pfiliberti/pico_tnc/pico-pcb/pcb.kicad_sch

## KiCad design pico-pcb/pcb.kicad_sch (2026-09-22)

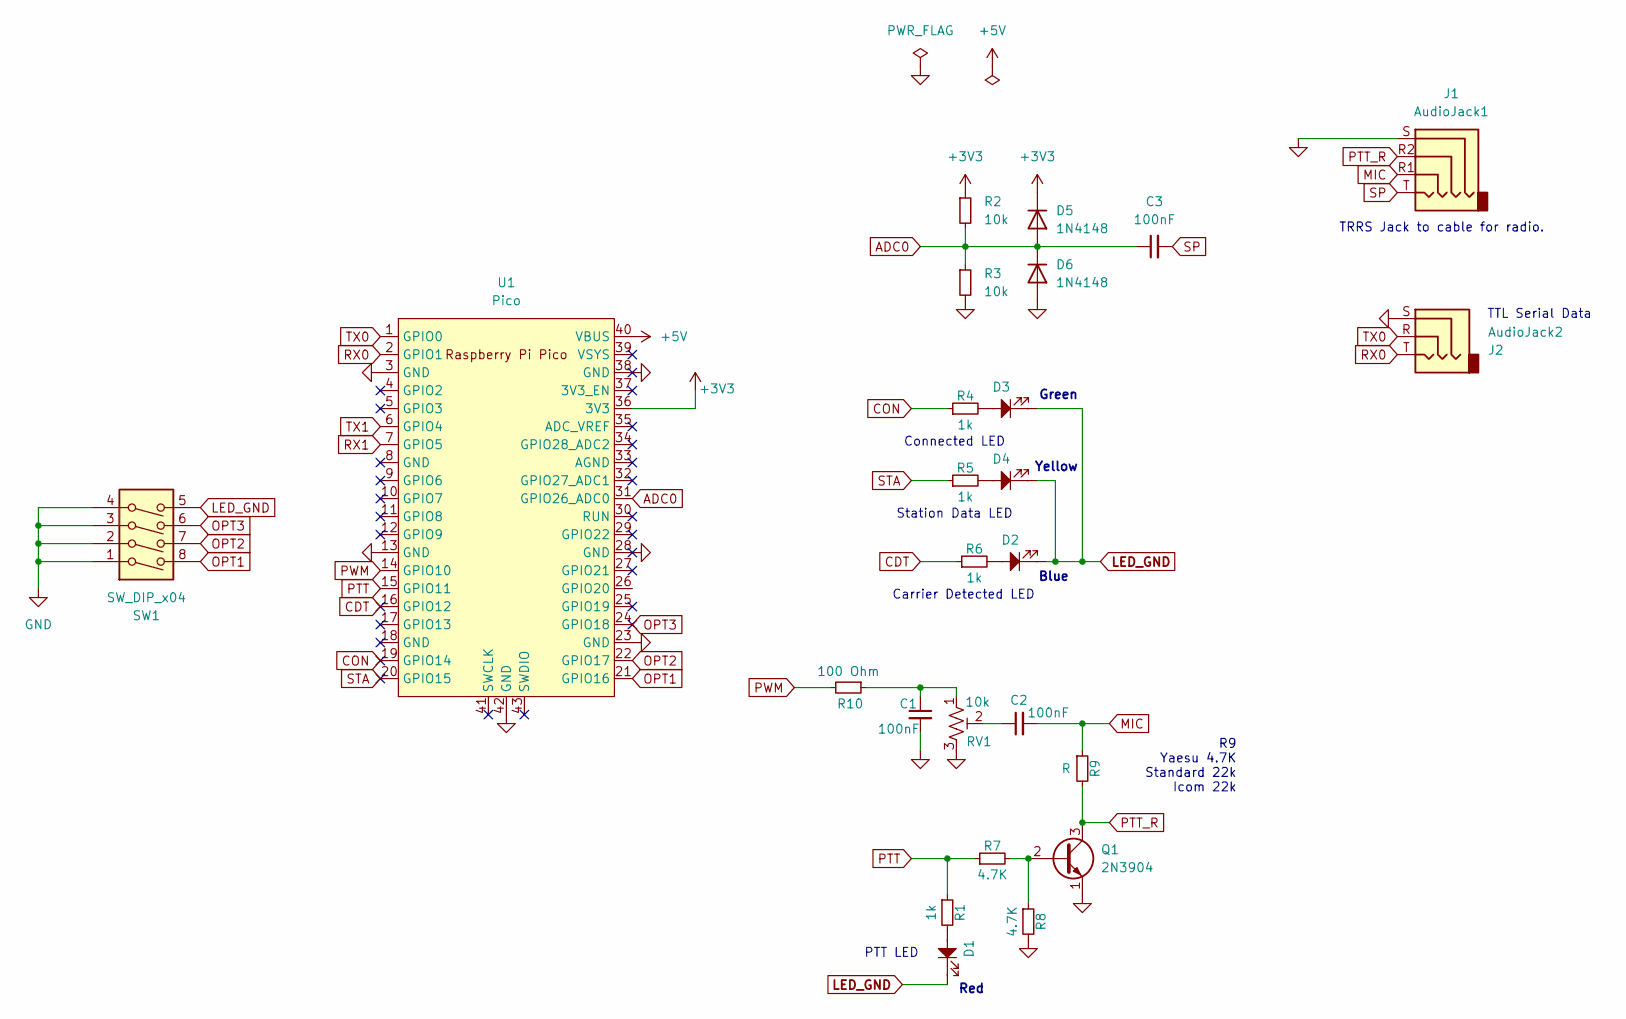
[picture p3: schematic pcb.kicad_sch]

Parts:
C1, C2, C3: 100nF; C_Disc_D3.0mm_W2.0mm_P2.50mm
D1, D2, D3, D4: LED_3mm; LED_D3.0mm_Horizontal_O1.27mm_Z2.0mm
D5, D6: 1N4148; D_DO-35_SOD27_P7.62mm_Horizontal
J1: AudioJack1; Jack_3.5mm_PJ320D_Horizontal
J2: AudioJack2; PJ-307
Q1: 2N3904; TO-92_Inline
R1, R4, R5, R6: 1k; R_Axial_DIN0204_L3.6mm_D1.6mm_P5.08mm_Horizontal
R2, R3: 10k; R_Axial_DIN0204_L3.6mm_D1.6mm_P5.08mm_Horizontal
R7, R8: 4.7K; R_Axial_DIN0204_L3.6mm_D1.6mm_P5.08mm_Horizontal
R9: R; R_Axial_DIN0204_L3.6mm_D1.6mm_P5.08mm_Horizontal
R10: 100 Ohm; R_Axial_DIN0204_L3.6mm_D1.6mm_P5.08mm_Horizontal
RV1: 10k; Potentiometer_Runtron_RM-063_Horizontal
SW1: SW_DIP_x04; SW_DIP_SPSTx04_Piano_CTS_Series194-4MSTN_W7.62mm_P2.54mm
U1: Pico; RPi_Pico_SMD_TH

Connections:
+3V3: D5.1 (K), R2.1, U1.36 (3V3)
+5V: U1.40 (VBUS)
ADC0: C3.1, D5.2 (A), D6.1 (K), R2.2, R3.1, U1.31 (GPIO26_ADC0)
CDT: R6.1, U1.16 (GPIO12)
CON: R4.1, U1.19 (GPIO14)
GND: C1.2, D6.2 (A), J1.S, J2.S, Q1.1 (E), R3.2, R8.2, RV1.3, SW1.1, SW1.2, SW1.3, SW1.4, U1.3 (GND), U1.13 (GND), U1.23 (GND), U1.28 (GND), U1.38 (GND), U1.42 (GND)
LED_GND: D1.1, D2.1, D3.1, D4.1, SW1.5
MIC: C2.2, J1.R1, R9.1
unnamed: C1.1, R10.1, RV1.1
unnamed: C2.1, RV1.2
unnamed: D1.2, R1.2
unnamed: D2.2, R6.2
unnamed: D3.2, R4.2
unnamed: D4.2, R5.2
unnamed: Q1.2 (B), R7.2, R8.1
OPT1: SW1.8, U1.21 (GPIO16)
OPT2: SW1.7, U1.22 (GPIO17)
OPT3: SW1.6, U1.24 (GPIO18)
PTT: R1.1, R7.1, U1.15 (GPIO11)
PTT_R: J1.R2, Q1.3 (C), R9.2
PWM: R10.2, U1.14 (GPIO10)
RX0: J2.T, U1.2 (GPIO1)
RX1: U1.7 (GPIO5)
SP: C3.2, J1.T
STA: R5.1, U1.20 (GPIO15)
TX0: J2.R, U1.1 (GPIO0)
TX1: U1.6 (GPIO4)

Notes on the sheet:
PTT LED
Carrier Detected LED
Yellow
Green
TRRS Jack to cable for radio.
Station Data LED
TTL Serial Data
Blue
Connected LED
R9 Yaesu 4.7K Standard 22k Icom 22k
Red
