pfiliberti/pico_tnc/pico_tnc/ax25.c

/*
Copyright (c) 2021, Kazuhisa Yokota, JN1DFF
All rights reserved.

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
THIS SOFTWARE IS PROVIDED BY THE COPYRIGHT HOLDERS AND CONTRIBUTORS "AS IS" AND
ANY EXPRESS OR IMPLIED WARRANTIES, INCLUDING, BUT NOT LIMITED TO, THE IMPLIED
WARRANTIES OF MERCHANTABILITY AND FITNESS FOR A PARTICULAR PURPOSE ARE
DISCLAIMED. IN NO EVENT SHALL <COPYRIGHT HOLDER> BE LIABLE FOR ANY
DIRECT, INDIRECT, INCIDENTAL, SPECIAL, EXEMPLARY, OR CONSEQUENTIAL DAMAGES
(INCLUDING, BUT NOT LIMITED TO, PROCUREMENT OF SUBSTITUTE GOODS OR SERVICES;
LOSS OF USE, DATA, OR PROFITS; OR BUSINESS INTERRUPTION) HOWEVER CAUSED AND
ON ANY THEORY OF LIABILITY, WHETHER IN CONTRACT, STRICT LIABILITY, OR TORT
(INCLUDING NEGLIGENCE OR OTHERWISE) ARISING IN ANY WAY OUT OF THE USE OF THIS
SOFTWARE, EVEN IF ADVISED OF THE POSSIBILITY OF SUCH DAMAGE.
*/

/*
    calculate CCITT-16 CRC using DMA CRC hardware
*/
#include <stdio.h>
#include "pico/stdlib.h"

#include "ax25.h"
#include "tnc.h" // Added by Codex


/* Input Queue to stack multiple incoming packets */
struct inQueue Ax25_In_Q[AX25_IN_MAXSIZE];
unsigned int Ax25_In_Head;
unsigned int Ax25_In_Tail;

//#ifdef RASPBERRYPI_PICO
#ifdef PICO_DEFAULT_UART

#include "hardware/dma.h"

#define OUT_INV (1 << 11)
#define OUT_REV (1 << 10)

int ax25_fcs(uint32_t crc, const uint8_t *data, int size)
{
    uint8_t dummy;
    int dma_chan = dma_claim_unused_channel(true);
    dma_channel_config c = dma_channel_get_default_config(dma_chan);

    channel_config_set_transfer_data_size(&c, DMA_SIZE_8);
    channel_config_set_write_increment(&c, false);
    channel_config_set_read_increment(&c, true);
    channel_config_set_dreq(&c, DREQ_FORCE);

    dma_channel_configure(
        dma_chan,
        &c,
        &dummy,
        data,
        size,
        false
    );

    // enable sniffer
    dma_sniffer_enable(dma_chan, 0x3, true);
    dma_hw->sniff_ctrl |= OUT_INV | OUT_REV;
    dma_hw->sniff_data = crc;
    dma_hw->sniff_data >>= 16;

    // start DMA
    dma_channel_start(dma_chan);

    // wait for finish
    dma_channel_wait_for_finish_blocking(dma_chan);
    dma_channel_unclaim(dma_chan);

    return dma_hw->sniff_data >> 16;
}

#else

#warning using C standard routine

#define CRC16_POLY 0x10811 /* G(x) = 1 + x^5 + x^12 + x^16 */

int ax25_fcs(uint32_t crc, const uint8_t packet[], int length)
{
    int i, j;

    if (length <= 0) return -1; // packet too short

    // calculate CRC x^16 + x^12 + x^5 + 1
    crc = 0xffff; /* initial value */
    for (i = 0; i < length; i++) {
	crc ^= packet[i];
	for (j = 0; j < 8; j++) {
	    if (crc & 1) crc ^= CRC16_POLY;
	    crc >>= 1;
	}
    }
    crc ^= 0xffff; // invert

    return crc;
}

#endif

bool ax25_callcmp(callsign_t *c, uint8_t *addr)
{
    for (int i = 0; i < 6; i++) {
        if (c->call[i] != (addr[i] >> 1)) return false;
    }

    if (c->ssid == ((addr[6] >> 1) & 0x0f)) return true;

    return false;
}

void ax25_mkax25addr(uint8_t *addr, callsign_t *c)
{
    uint8_t *s = addr;

    for (int i = 0; i < 6; i++) {
        *s++ = c->call[i] << 1;
    }

    // SSID
    *s = (c->ssid << 1) | 0x60;
}

bool ax25_ui(uint8_t *packet, int len)
{
    int i;

    i = AX25_ADDR_LEN - 1; // SSID
    while (i < len) {
        if (packet[i] & 1) break; // address extension bit
        i += AX25_ADDR_LEN;
    }
    i++;

    if (i + 2 > len) return false; // no control and  PID field

    return packet[i] == 0x03 && packet[i+1] == 0xf0; // true if UI packet
}

void ax25_init_Q(void)
{
    Ax25_In_Head = 0;
    Ax25_In_Tail = 0;
}

bool ax25_InQ_HasRoom(void)
{
  int next = Ax25_In_Head + 1;
  if(next >= AX25_IN_MAXSIZE) 
    next = 0;

  if(next == Ax25_In_Tail)
    return false;
  else
    return true;
}

void ax25_InQ_Insert(const uint8_t packet[], int length)
{
#if CODEX_RX_DIAGNOSTICS
    // Added by Codex
    extern struct {
      unsigned int rx_queue_inserted;
      unsigned int rx_queue_dropped_full;
      unsigned int rx_queue_started;
      unsigned int rx_queue_completed;
      unsigned int rx_queue_restarts;
      unsigned int rx_queue_max_depth;
      unsigned int rx_packet_max_len;
      unsigned int adc_dma_overruns;
      unsigned int tx_out_overflows;
    } codex_diag;

    codex_diag.rx_queue_inserted++;
    if ((unsigned int)length > codex_diag.rx_packet_max_len) codex_diag.rx_packet_max_len = length;
#endif

    /* use length - 2 to remove crc bytes */
    for(int x=0; x < length-2; x++)
    { 
        Ax25_In_Q[Ax25_In_Head].data[x] = packet[x]; /*Socket_Data_In[x]; */
    }

    /* Tncemu logic needs an extra byte in the length do to processing logic! */
    Ax25_In_Q[Ax25_In_Head].count = length-1;

    if(++Ax25_In_Head >= AX25_IN_MAXSIZE) 
    Ax25_In_Head = 0;
}

void ax25_InQ_Remove(void)
{
  if(++Ax25_In_Tail >= AX25_IN_MAXSIZE) 
    Ax25_In_Tail = 0;
}

bool ax25_InQ_HasData(void)
{
  if(Ax25_In_Head != Ax25_In_Tail)
    return(true);
  else
    return(false);
}
